Electroner/ModernWood/PCB/Docs/Schematic.pdf

### 1 VCC GND GNDVCC ESP32-S3HOLE74HC154D GND GND GND GND GND 1K 1K

1K 1K GNDVCC GND GND GND GND VCC

1M 4M GND GND GND VCC

1 VCC GND 1K VCC GND GND VCC GND VCC GND VCC GND VCC GND VCC GND VCC GND VCC GND VCC GND VCC GND VCC

FS8205

### 1M 2M GND 1M 2M GND

CHERRY-MX

PIN-1 SW1 PIN-2 SW2 U$1 CHERRY-MX

PIN-1 SW1 PIN-2 SW2 U$2 CHERRY-MX

PIN-1 SW1 PIN-2 SW2 U$3 CHERRY-MX

PIN-1 SW1 PIN-2 SW2 U$4 CHERRY-MX

PIN-1 SW1 PIN-2 SW2 U$5 CHERRY-MX

PIN-1 SW1 PIN-2 SW2 U$6 CHERRY-MX

PIN-1 SW1 PIN-2 SW2 U$7 CHERRY-MX

PIN-1 SW1 PIN-2 SW2 U$8 CHERRY-MX

PIN-1 SW1 PIN-2 SW2 U$9 CHERRY-MX

PIN-1 SW1 PIN-2 SW2 U$10 CHERRY-MX

PIN-1 SW1 PIN-2 SW2 U$11 CHERRY-MX

PIN-1 SW1 PIN-2 SW2 U$12 CHERRY-MX

PIN-1 SW1 PIN-2 SW2 U$13 CHERRY-MX

PIN-1 SW1 PIN-2 SW2 U$14 CHERRY-MX

PIN-1 SW1 PIN-2 SW2 U$15 CHERRY-MX

PIN-1 SW1 PIN-2 SW2 U$16 CHERRY-MX

PIN-1 SW1 PIN-2 SW2 U$17 CHERRY-MX

PIN-1 SW1 PIN-2 SW2 U$18 CHERRY-MX

PIN-1 SW1 PIN-2 SW2 U$19 CHERRY-MX

PIN-1 SW1 PIN-2 SW2 U$20 CHERRY-MX

PIN-1 SW1 PIN-2 SW2 U$21 CHERRY-MX

PIN-1 SW1 PIN-2 SW2 U$22 CHERRY-MX

PIN-1 SW1 PIN-2 SW2 U$23 CHERRY-MX

PIN-1 SW1 PIN-2 SW2 U$24 CHERRY-MX

PIN-1 SW1 PIN-2 SW2 U$25 CHERRY-MX

PIN-1 SW1 PIN-2 SW2 U$26 CHERRY-MX

PIN-1 SW1 PIN-2 SW2 U$27 CHERRY-MX

PIN-1 SW1 PIN-2 SW2 U$28 CHERRY-MX

PIN-1 SW1 PIN-2 SW2 U$29 CHERRY-MX

PIN-1 SW1 PIN-2 SW2 U$30 CHERRY-MX

PIN-1 SW1 PIN-2 SW2 U$31 CHERRY-MX

PIN-1 SW1 PIN-2 SW2 U$32 CHERRY-MX

PIN-1 SW1 PIN-2 SW2 U$33 CHERRY-MX

PIN-1 SW1 PIN-2 SW2 U$34 CHERRY-MX

PIN-1 SW1 PIN-2 SW2 U$35 CHERRY-MX

PIN-1 SW1 PIN-2 SW2 U$36 CHERRY-MX

PIN-1 SW1 PIN-2 SW2 U$37 CHERRY-MX

PIN-1 SW1 PIN-2 SW2 U$38 CHERRY-MX

PIN-1 SW1 PIN-2 SW2 U$39 CHERRY-MX

PIN-1 SW1 PIN-2 SW2 U$40 CHERRY-MX

PIN-1 SW1 PIN-2 SW2 U$41 CHERRY-MX

PIN-1 SW1 PIN-2 SW2 U$42 CHERRY-MX

PIN-1 SW1 PIN-2 SW2 U$43 CHERRY-MX

PIN-1 SW1 PIN-2 SW2 U$44 CHERRY-MX

PIN-1 SW1 PIN-2 SW2 U$45 CHERRY-MX

PIN-1 SW1 PIN-2 SW2 U$46 CHERRY-MX

PIN-1 SW1 PIN-2 SW2 U$47 CHERRY-MX

PIN-1 SW1 PIN-2 SW2 U$48 CHERRY-MX

PIN-1 SW1 PIN-2 SW2 U$49 CHERRY-MX

PIN-1 SW1 PIN-2 SW2 U$50 CHERRY-MX

PIN-1 SW1 PIN-2 SW2 U$51 CHERRY-MX

PIN-1 SW1 PIN-2 SW2 U$52 CHERRY-MX

PIN-1 SW1 PIN-2 SW2 U$53 CHERRY-MX

PIN-1 SW1 PIN-2 SW2 U$54 CHERRY-MX

PIN-1 SW1 PIN-2 SW2 U$55 CHERRY-MX

PIN-1 SW1 PIN-2 SW2 U$56 CHERRY-MX

PIN-1 SW1 PIN-2 SW2 U$57 CHERRY-MX

PIN-1 SW1 PIN-2 SW2 U$58 CHERRY-MX

PIN-1 SW1 PIN-2 SW2 U$59 CHERRY-MX

PIN-1 SW1 PIN-2 SW2 U$60 CHERRY-MX

PIN-1 SW1 PIN-2 SW2 U$61 CHERRY-MX

PIN-1 SW1 PIN-2 SW2 U$62 CHERRY-MX

PIN-1 SW1 PIN-2 SW2 U$63 CHERRY-MX

PIN-1 SW1 PIN-2 SW2 U$64 CHERRY-MX

PIN-1 SW1 PIN-2 SW2 U$65 CHERRY-MX
PIN-1 SW1 PIN-2 SW2 U$66

CHERRY-MX
PIN-1 SW1 PIN-2 SW2 FN_KEY

CHERRY-MX

PIN-1 SW1 PIN-2 SW2 U$68 CHERRY-MX

PIN-1 SW1 PIN-2 SW2 U$69 CHERRY-MX

PIN-1 SW1 PIN-2 SW2 U$70 CHERRY-MX

PIN-1 SW1 PIN-2 SW2 U$71 CHERRY-MX

PIN-1 SW1 PIN-2 SW2 U$72 CHERRY-MX

PIN-1 SW1 PIN-2 SW2 U$73 CHERRY-MX

PIN-1 SW1 PIN-2 SW2 U$74 CHERRY-MX

PIN-1 SW1 PIN-2 SW2 U$75 CHERRY-MX

PIN-1 SW1 PIN-2 SW2 U$76 CHERRY-MX

PIN-1 SW1 PIN-2 SW2 U$77 CHERRY-MX

PIN-1 SW1 PIN-2 SW2 U$78 CHERRY-MX

PIN-1 SW1 PIN-2 SW2 U$79 CHERRY-MX

PIN-1 SW1 PIN-2 SW2 U$80 CHERRY-MX

PIN-1 SW1 PIN-2 SW2 U$81 CHERRY-MX

PIN-1 SW1 PIN-2 SW2 U$82 CHERRY-MX

PIN-1 SW1 PIN-2 SW2 U$83 CHERRY-MX

PIN-1 SW1 PIN-2 SW2 U$84 CHERRY-MX

PIN-1 SW1 PIN-2 SW2 U$85 CHERRY-MX

PIN-1 SW1 PIN-2 SW2 U$86 CHERRY-MX

PIN-1 SW1 PIN-2 SW2 U$87 CHERRY-MX

PIN-1 SW1 PIN-2 SW2 U$88 CHERRY-MX

PIN-1 SW1 PIN-2 SW2 U$89 CHERRY-MX

PIN-1 SW1 PIN-2 SW2 U$90 CHERRY-MX

PIN-1 SW1 PIN-2 SW2 U$91 CHERRY-MX

PIN-1 SW1 PIN-2 SW2 U$92 CHERRY-MX

PIN-1 SW1 PIN-2 SW2 U$93 CHERRY-MX PIN-1 SW1 PIN-2 SW2 ENTERDUPLICADO

CHERRY-MX

# PIN-1 SW1 PIN-2 SW2 PUNTODUPLICADO

CHERRY-MX

PIN-1 SW1 PIN-2 SW2 DUPLICADO1 CHERRY-MX

PIN-1 SW1 PIN-2 SW2 DUPLICADO2 CHERRY-MX

PIN-1 SW1 PIN-2 SW2 DUPLICADO3 CHERRY-MX

PIN-1 SW1 PIN-2 SW2 DUPLICADO4 CHERRY-MX

PIN-1 SW1 PIN-2 SW2 DUPLICADO5 CHERRY-MX

PIN-1 SW1 PIN-2 SW2 DUPLICADO6 CHERRY-MX

PIN-1 SW1 PIN-2 SW2 DUPLICADO7 CHERRY-MX

PIN-1 SW1 PIN-2 SW2 DUPLICADO8 CHERRY-MX

PIN-1 SW1 PIN-2 SW2 DUPLICADO9 CHERRY-MX

PIN-1 SW1 PIN-2 SW2 DUPLICADO10

# 3 12 4 GND_2

1 3V3

### 2 EN

### 3 IO4

### 4 IO5

### 5 IO6

### 6 IO7

### 7 IO15

### 8 IO16

9 IO17 10 IO18 11 IO8 12 IO19 13 IO20 14 IO3 15 IO46 16 IO9 17 IO10 18 IO11 19 IO12 20 IO13 21 IO14 22 IO21 23 IO47 24 IO48 25 IO45 26 IO0 27 IO35 28 IO36 29 IO37 30 IO38 31 IO39 32 IO40 33 IO41 34 IO42 35 RXD0 36 TXD0 37 IO2 38 IO1 39 GND_3 40 GND 41 U1 D1 D2 D3 D4 D5 D6 D7 D8 D9 D10 D11 D12 D13 D14 D15 D16 D17 D18 D19 D20 D21 D22 D23 D24 D25 D26 D27 D28 D29 D30 D31 D32 D33 D34 D35 D36 D37 D38 D39 D40 D41 D42 D43 D44 D45 D46 D47 D48 D49 D50 D51 D52 D53 D54 D55 D56 D57 D58 D59 D60 D61 D62 D63 D64 D65 D66 D67 D68 D69 D70 D71 D72 D73 D74 D75 D76 D77 D78 D79 D80 D81 D82 D83 D84 D85 D86 D87 D88 D90 D91 D92 D93

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
10 11

11 13

12 14

13 15

14 16

15 17 G1 18 G2 19 D

### 20 C 21 B 22 A

# 23 GND 12 VCC 24 U$94

4

3

2

# 1 USB TEMP

### 1 PROG 2 GND

### 3 VCC

## 4 BAT

### 5 STDBY

### 6 CHRG

### 7 CE

### 8 U$95 VCC

### 5 GND

### 6 TD

### 4 OD 1 OC CS

3

2

2

### 1 BATTERY

8

7

6

5

4

3

2

# 1 SCREEN VIN

### 1 GND

## 2 EN

### 3 NC 4 VOUT

### 5 U2 ME6211C33M5G

3 12 4

1

2

3

4 BOOT LED_VDD LED_DI LED_GND LED_DO WS2812B5050 LED_VDD LED_DI LED_GND LED_DO LED_VDD LED_DI LED_GND LED_DO LED_VDD LED_DI LED_GND LED_DO LED_VDD LED_DI LED_GND LED_DO LED_VDD LED_DI LED_GND LED_DO LED_VDD LED_DI LED_GND LED_DO LED_VDD LED_DI LED_GND LED_DO LED_VDD LED_DI LED_GND LED_DO LED_VDD LED_DI LED_GND LED_DO

1

2*2

3

6

4 Q2 MUX13 MUX13 MUX13 MUX10 MUX10 MUX10 MUX1 MUX1 MUX1 MUX2 MUX2 MUX2 MUX4 MUX4 MUX4 MUX5 MUX5 MUX5 MUX6 MUX6 MUX6 MUX7 MUX7 MUX7 MUX8 MUX8 MUX8 MUX9 MUX9 MUX9 MUX0 MUX0 MUX0 MUX11 MUX11 MUX11 MUX3 MUX3 MUX3 MUX14 MUX14 MUX14 MUX15 MUX15 MUX15 MUX12 MUX12 MUX12 E4 E4 E4 E0 E0 E0 E1 E1 E1 E3 E3 E3 E5 E5 E5 E2 E2 E2

COD0 COD1 COD0 COD1 COD2 COD2COD3 COD3 RX RX TX TX INVCC INVCC INVCC INVCC D+ D+ D- D- CHRG CHRG STDBY STDBY B- B- TPPROG DWCS DWVCC SCL SCL SDA SDA RES RES DC DC CS CS BLK BLK BATLEVEL BATLEVEL KEY_FN

KEY_FN LEDS LEDS PROG PROG B+ B+B+ B+ B+ B+ STDBY_3 CHRG_3 STDBY_3 CHRG_3 ModernWood

6 Document 1 By Carlos Lopez Martinez LEDS Main Chip and Special buttons Connection headers Power and Battery 4 to 16 Mux Main Keys TP4056 DW01A Lithium Protection R2 R1 R3 R4

R5 R6 R7 Date: Sheet: REV: TITLE: Document Number: 22/02/2024 1:00 1/1 R8 R9 R10 R11

io 0

io 0

io 0

io 0

io 0

io 0

io 0

io 0

io 0

io 0

io 0

io 0

io 0

io 0

io 0

io 0

io 0

io 0

io 0

io 0

io 0

io 0

io 0

io 0

io 0

io 0

io 0

io 0

io 0

io 0

io 0

io 0

io 0

io 0

io 0

io 0

io 0

io 0

io 0

io 0

io 0

io 0

io 0

io 0

io 0

io 0

io 0

io 0

io 0

io 0

io 0

io 0

io 0

io 0

io 0

io 0

io 0

io 0

io 0

io 0

io 0

io 0

io 0

io 0

io 0

io 0

io 0

io 0

io 0

io 0

io 0

io 0

io 0

io 0

io 0

io 0

io 0

io 0

io 0

io 0

io 0

io 0

io 0

io 0

io 0

io 0

io 0

io 0

io 0

io 0

io 0

io 0

io 0

io 0

io 0

io 0

io 0

io 0

io 0

io 0

io 0

io 0

io 0

io 0

io 0

io 0

io 0

io 0

io 0

io 0

io 0

io 0

io 0

io 0

io 0

io 0

io 0

io 0

io 0

io 0

io 0

io 0

io 0

io 0

io 0

io 0

io 0

io 0

io 0

io 0

io 0

io 0

io 0

io 0

io 0

io 0

io 0

io 0

io 0

io 0

io 0

io 0

io 0

io 0

io 0

io 0

io 0

io 0

io 0

io 0

io 0

io 0

io 0

io 0

io 0

io 0

io 0

io 0

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

# sup 0 pwr 0 in 0 pwr 0 out 0

sup 0

# sup 0 pwr 0 in 0 pwr 0 out 0

sup 0

# sup 0 pwr 0 in 0 pwr 0 out 0

sup 0

# sup 0 pwr 0 in 0 pwr 0 out 0

sup 0

# sup 0 pwr 0 in 0 pwr 0 out 0

sup 0

sup 0 pas 0

pas 0 pas 0

pas 0

pas 0

pas 1 pas 1 pas 1 pas 1 sup 0 pas 1 pas 1 pas 1 pas 1 sup 0
