Electroner/ModernWood/Electronics/ESP32S3/ESP32-S3_DevKitC-1_pinlayout.jpg

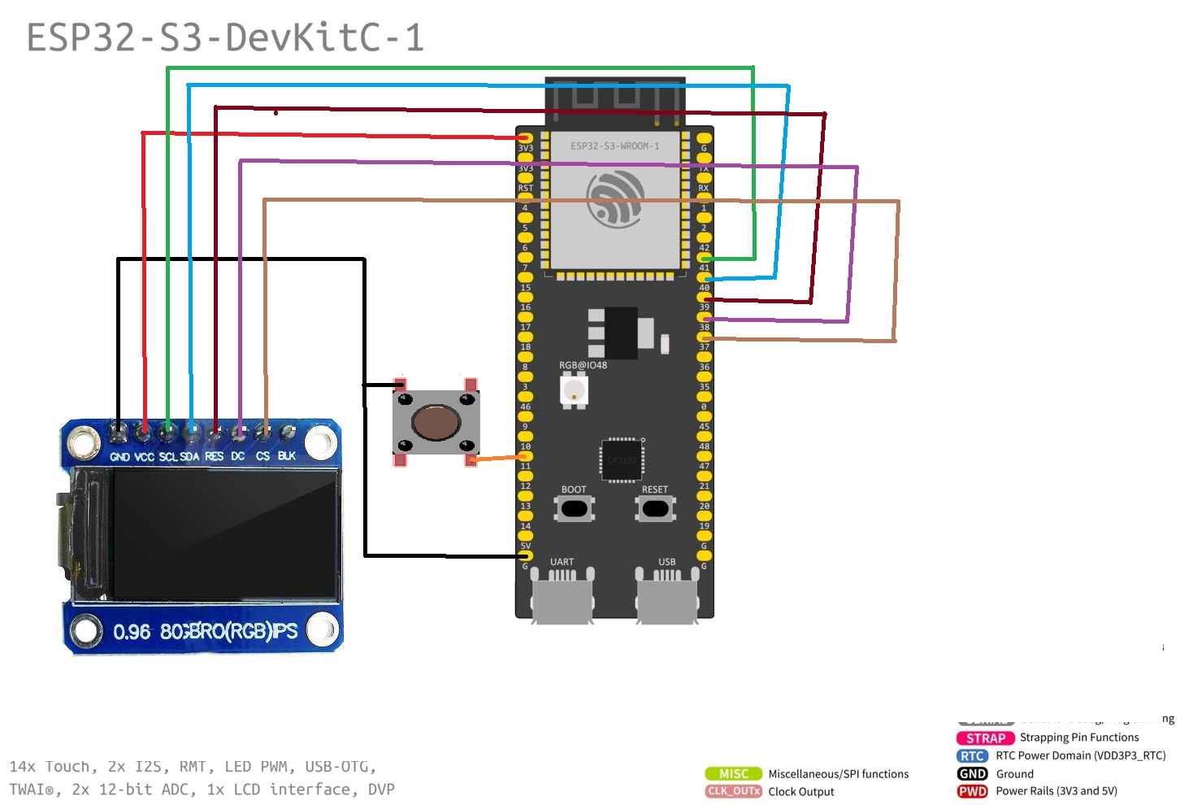
Electronics/ESP32S3/ESP32-S3_DevKitC-1_pinlayout.jpg
