Electroner/ModernWood/Images/Product/12N.jpg

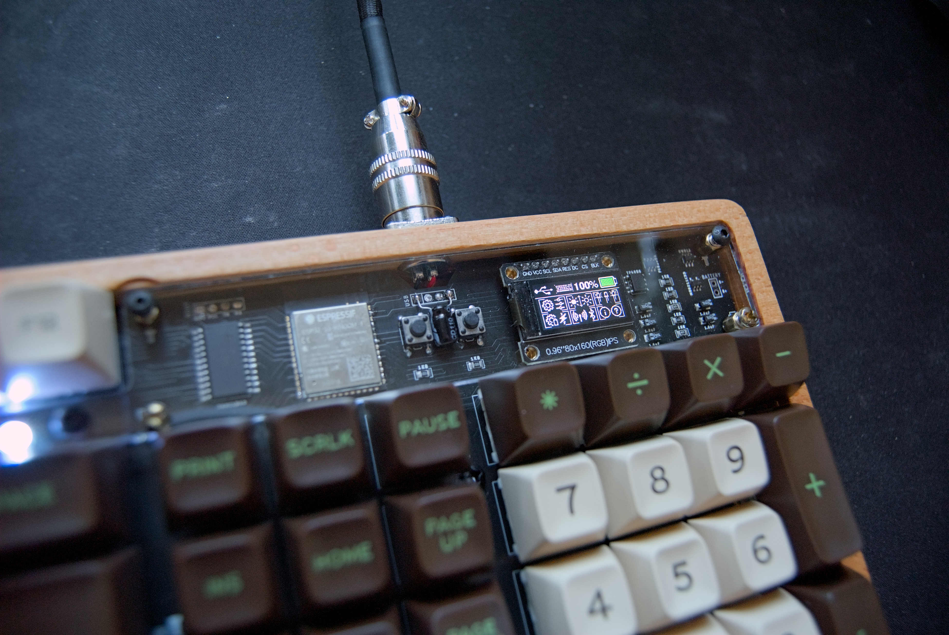
Images/Product/12N.jpg
