Electroner/ModernWood/Images/Product/13N.jpg

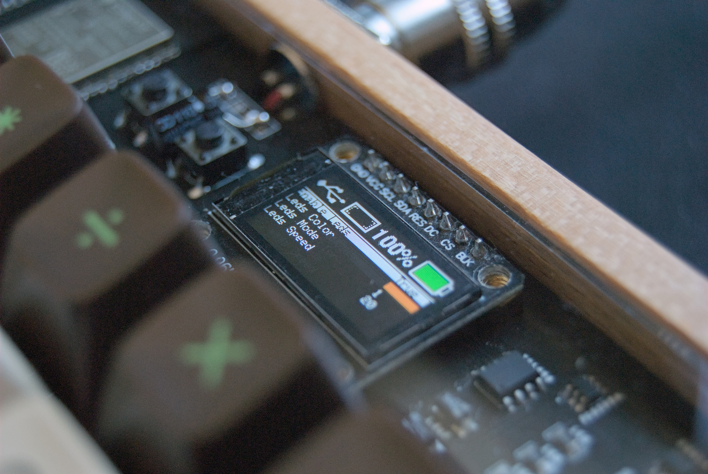
Images/Product/13N.jpg
