Electroner/ModernWood/Images/Product/15N.jpg

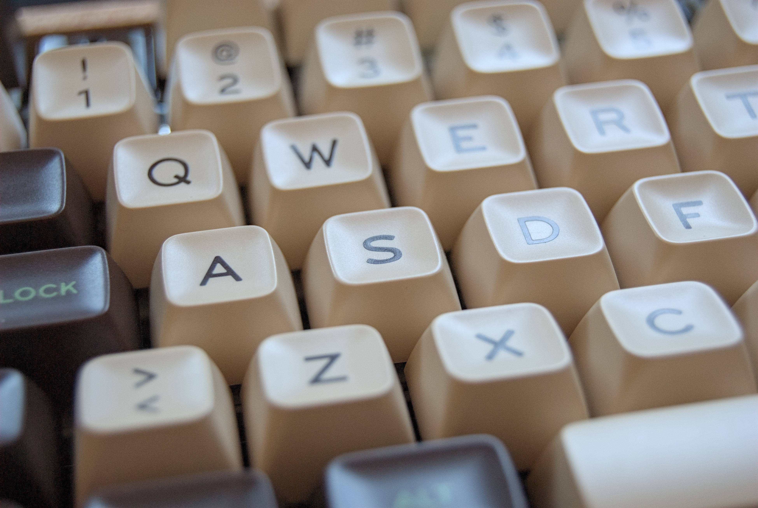
Images/Product/15N.jpg
