Electroner/ModernWood/Images/Product/16N.jpg

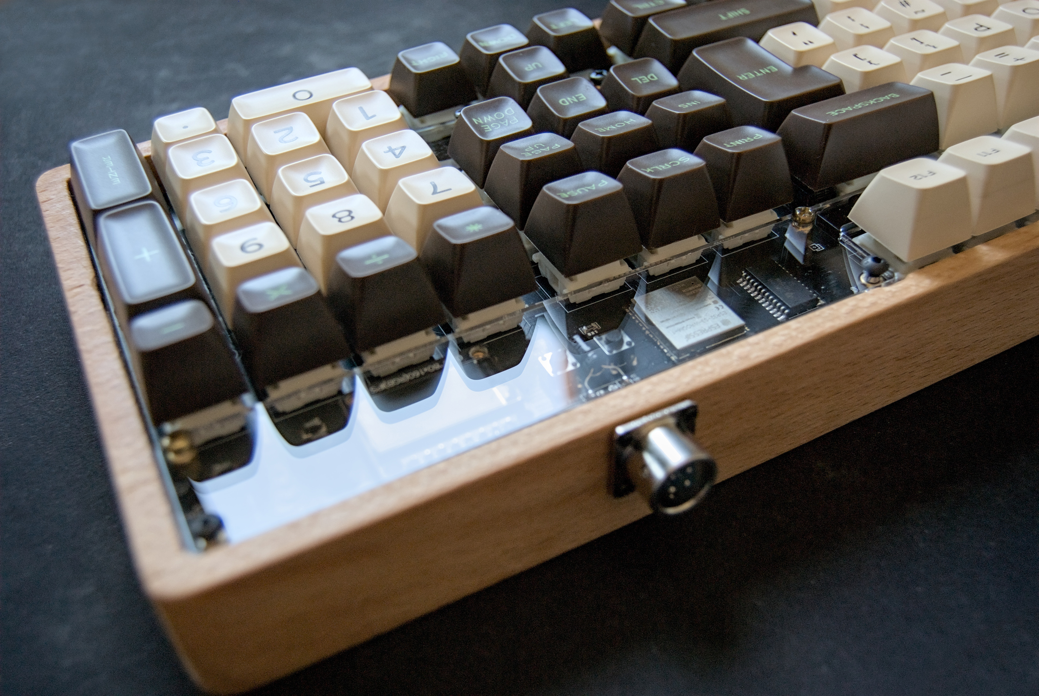
Images/Product/16N.jpg
