Electroner/ModernWood/Planos/Planos Acotados.pdf

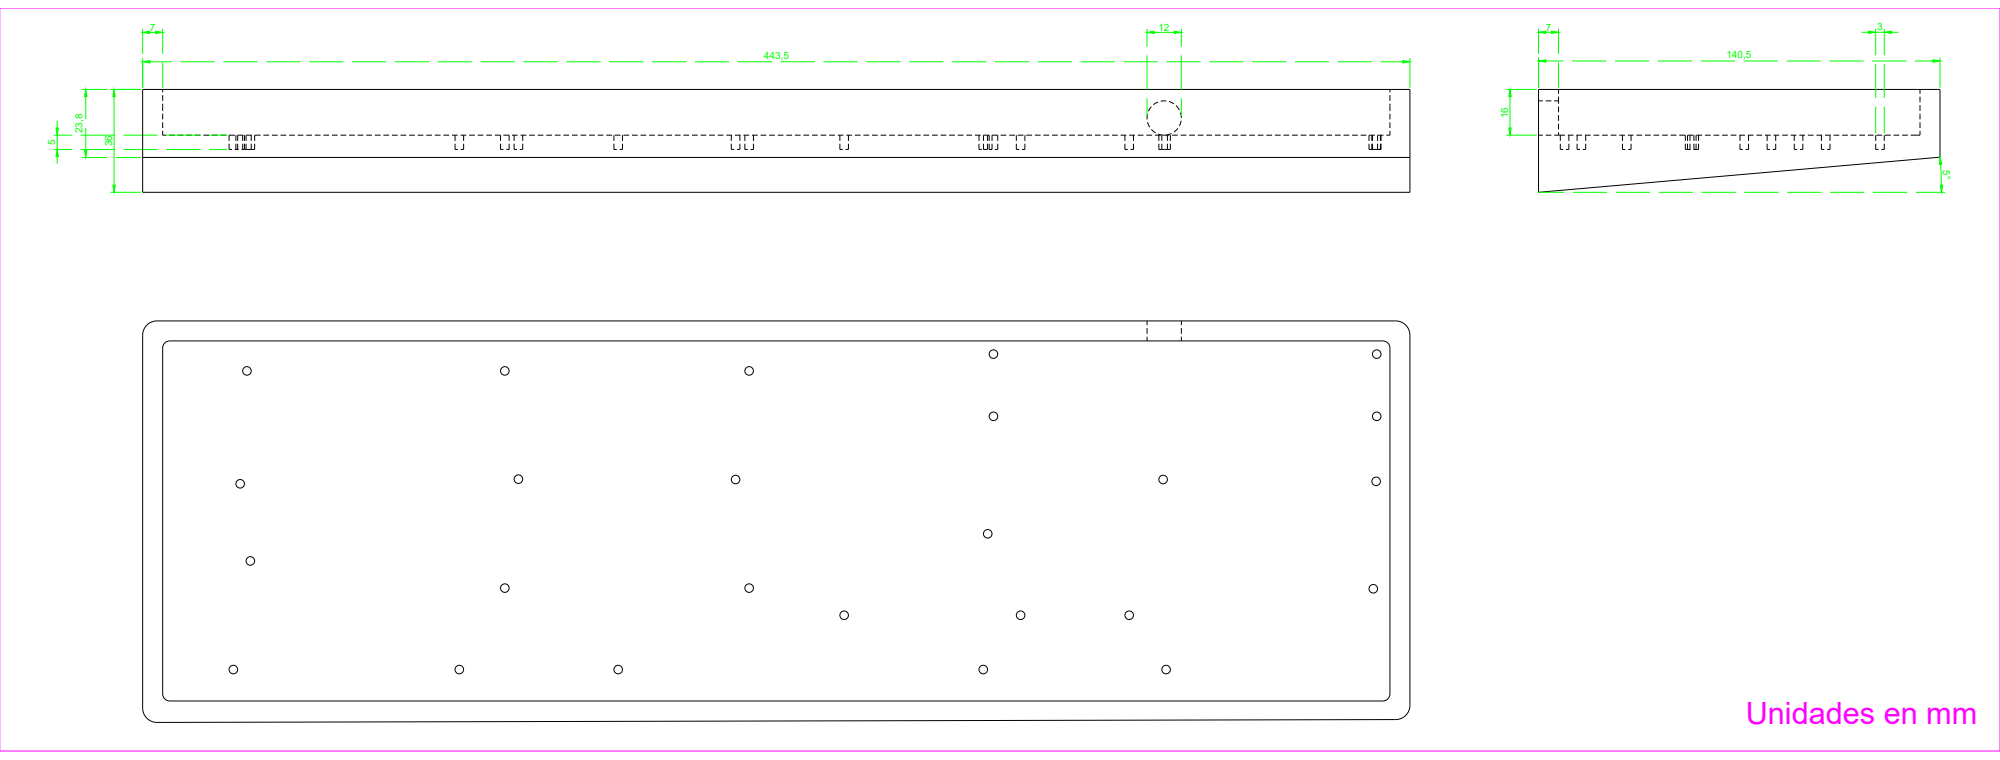
[picture p34: page 1]

5° Unidades en mm
