Electroner/ModernWood/ModernWood/include/Images.h

#pragma once
static const uint8_t image_Icon[6400] PROGMEM= {
0x00,0x00,0x00,0x00,0x00,0x00,0x00,0x00,0x00,0x00
,0x80,0x00,0x00,0x00,0x00,0x00,0x00,0x20,0x00,0x00
,0xe0,0x00,0x00,0x00,0x00,0x00,0x00,0x60,0x00,0x00
,0xf0,0x00,0x00,0x00,0x00,0x00,0x00,0xe0,0x00,0x00
,0xf8,0x00,0x00,0x00,0x00,0x00,0x01,0xe0,0x00,0x00
,0xfc,0x00,0x00,0x00,0x00,0x00,0x03,0xe0,0x00,0x00
,0xfe,0x00,0x00,0x00,0x00,0x00,0x0f,0xe0,0x00,0x00
,0xff,0x00,0x00,0x00,0x00,0x00,0x1f,0xe0,0x00,0x00
,0xff,0x80,0x00,0x00,0x00,0x00,0x3f,0xe0,0x00,0x00
,0xff,0xc0,0x00,0x00,0x00,0x00,0x7f,0xe0,0x01,0xff
,0xff,0xe0,0x00,0x00,0x00,0x00,0xff,0xe0,0x01,0xff
,0xff,0xf0,0x00,0x00,0x00,0x01,0xff,0xe0,0x01,0xff
,0xff,0xf8,0x00,0x00,0x00,0x03,0xff,0xe0,0x01,0xff
,0xff,0xfc,0x00,0x00,0x00,0x07,0xff,0xe0,0x01,0xff
,0xff,0xfe,0x00,0x00,0x00,0x0f,0xff,0xe0,0x01,0xff
,0xff,0xff,0x00,0x00,0x00,0x1f,0xff,0xe0,0x01,0xff
,0xff,0xff,0x80,0x00,0x00,0x3f,0xff,0xe0,0x01,0xff
,0xff,0xff,0xc0,0x00,0x00,0x7f,0xff,0xe0,0x01,0xff
,0xff,0xff,0xe0,0x00,0x00,0xff,0xff,0xe0,0x01,0xff
,0xff,0xff,0xf8,0x00,0x01,0xff,0xff,0xe0,0x01,0xff
,0xff,0xff,0xfc,0x00,0x03,0xff,0xff,0xe0,0x01,0xff
,0xff,0xbf,0xfe,0x00,0x07,0xff,0xbf,0xe0,0x01,0xff
,0xff,0x9f,0xff,0x00,0x1f,0xff,0x3f,0xe0,0x01,0xff
,0xff,0x8f,0xff,0x80,0x3f,0xfe,0x3f,0xe0,0x01,0xff
,0xff,0x87,0xff,0xc0,0x7f,0xfc,0x3f,0xe0,0x01,0xff
,0xff,0x83,0xff,0xe0,0xff,0xf8,0x3f,0xe0,0x01,0xff
,0xff,0x81,0xff,0xf1,0xff,0xf0,0x3f,0xe0,0x01,0xff
,0xff,0x80,0xff,0xfb,0xff,0xe0,0x3f,0xe0,0x01,0xff
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
    const uint8_t y = 4;
    const uint8_t width = 13;
    const uint8_t height = 17;
}Connection_display_image;

const struct KeyboardFN_display_image{
    const uint8_t x = 40;
    const uint8_t y = 5;
    const uint8_t width = 32;
    const uint8_t height = 15;
}KeyboardFN_display_image;

const struct DisplaydFN_display_image{
    const uint8_t x = 40;
    const uint8_t y = 5;
    const uint8_t width = 32;
    const uint8_t height = 15;
}DisplaydFN_display_image;

//MENU

const struct Menu_Config_display_image{
    const uint8_t x = 5;
    const uint8_t y = 27;
    const uint8_t width = 48;
    const uint8_t height = 24;
}Menu_Config_display_image;

const struct Menu_Brightness_display_image{
    const uint8_t x = 56;
    const uint8_t y = 27;
    const uint8_t width = 48;
    const uint8_t height = 24;
}Menu_Brightness_display_image;

const struct Menu_Leds_display_image{
    const uint8_t x = 107;
    const uint8_t y = 27;
    const uint8_t width = 48;
    const uint8_t height = 24;
}Menu_Leds_display_image;

const struct Menu_Energy_display_image{
    const uint8_t x = 5;
    const uint8_t y = 53;
    const uint8_t width = 48;
    const uint8_t height = 24;
}Menu_Energy_display_image;

const struct Menu_Connection_display_image{
    const uint8_t x = 56;
    const uint8_t y = 53;
    const uint8_t width = 48;
    const uint8_t height = 24;
}Menu_Connection_display_image;

const struct Menu_InfoHelp_display_image{
    const uint8_t x = 107;
    const uint8_t y = 53;
    const uint8_t width = 48;
    const uint8_t height = 24;
}Menu_InfoHelp_display_image;

const struct General_Screen_display{
    const uint8_t x = 0;
    const uint8_t y = 26;
    const uint8_t width = 160;
    const uint8_t height = 53;
}General_Screen_display;

//The max size on the option value is 36 pixels
const struct Option_Value_Position_display{
    const uint8_t x = 125;
    const uint8_t y = 26;
}Option_Value_Position_display;
